GunnerLeo/Cryptid-Sledgfire-Pump-Action-Clip-Fed-Conversion/Cryptid Clips STL Files/Mega Clips/10 Shot Mega.stl

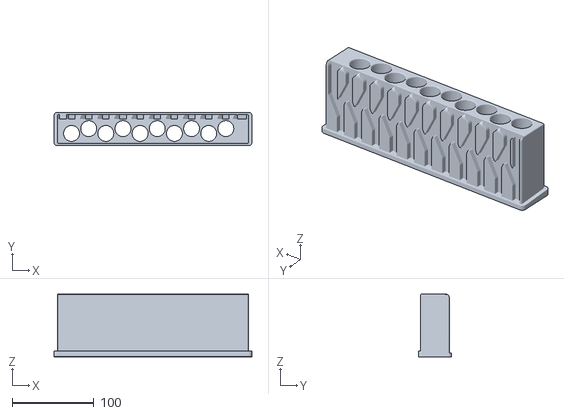
[picture p20: CAD file, 2022-12-31]
Cryptid Clips STL Files/Mega Clips/10 Shot Mega.stl
242.4 x 41.0 x 77.0
