GunnerLeo/Cryptid-Sledgfire-Pump-Action-Clip-Fed-Conversion/Cryptid Clips STL Files/Single Shot Clips/10 Shot Single.stl

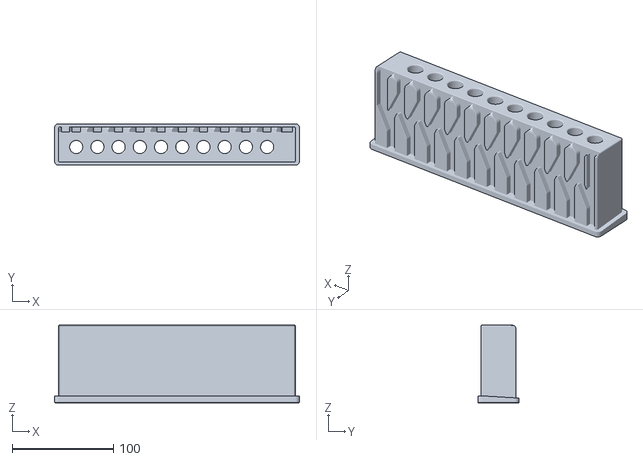
[picture p21: CAD file, 2022-12-31]
Cryptid Clips STL Files/Single Shot Clips/10 Shot Single.stl
242.4 x 41.0 x 77.0
