GunnerLeo/Cryptid-Sledgfire-Pump-Action-Clip-Fed-Conversion/Cryptid STL Files/Manacles.stl

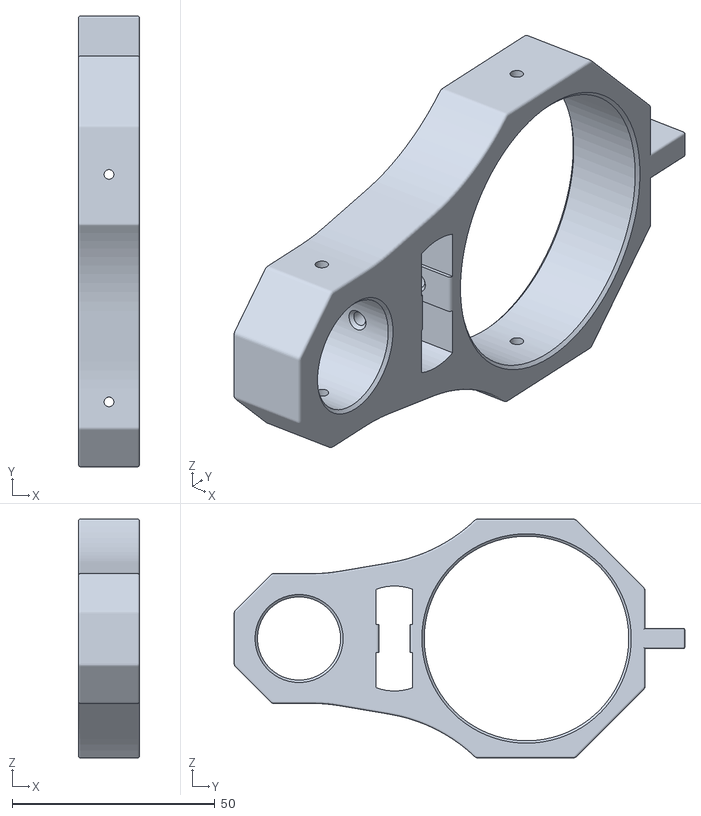
[picture p22: CAD file, 2022-12-30]
Cryptid STL Files/Manacles.stl
15.0 x 111.1 x 58.9
