GunnerLeo/Cryptid-Sledgfire-Pump-Action-Clip-Fed-Conversion/Cryptid STL Files/LongHinge1.stl

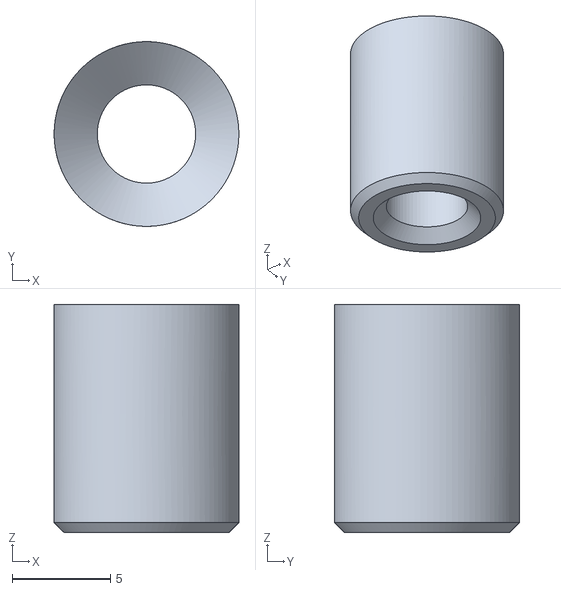
[picture p23: CAD file, 2022-12-30]
Cryptid STL Files/LongHinge1.stl
9.40 x 9.40 x 11.6
