GunnerLeo/Cryptid-Sledgfire-Pump-Action-Clip-Fed-Conversion/Cryptid STL Files/Latch Replacement.stl

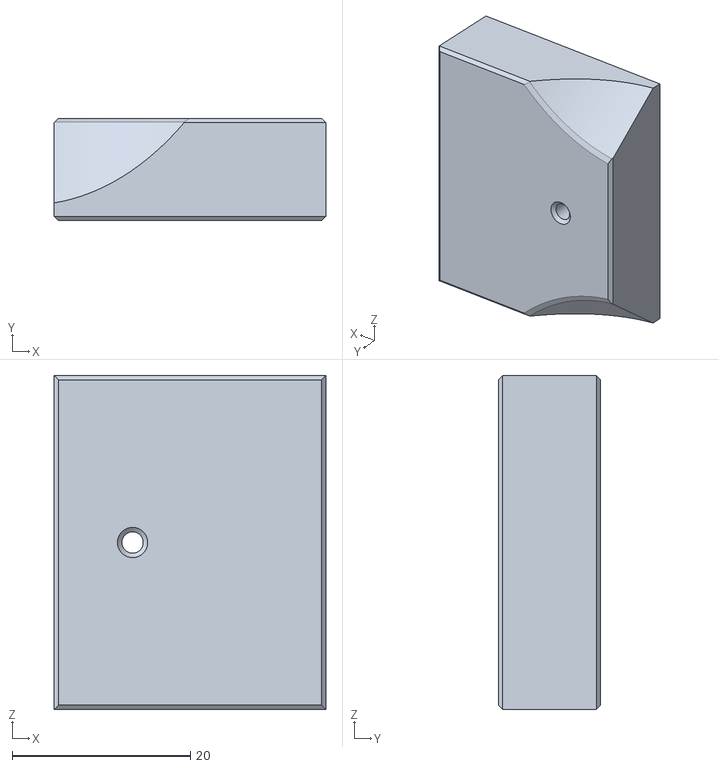
[picture p24: CAD file, 2022-12-30]
Cryptid STL Files/Latch Replacement.stl
30.5 x 11.5 x 37.5
