GunnerLeo/Cryptid-Sledgfire-Pump-Action-Clip-Fed-Conversion/Cryptid STL Files/ConnectorArm.stl

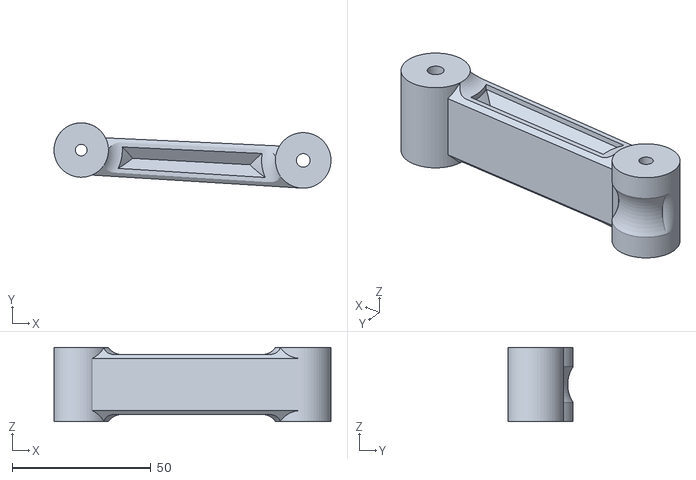
[picture p25: CAD file, 2022-12-30]
Cryptid STL Files/ConnectorArm.stl
99.7 x 23.5 x 26.7
