GunnerLeo/Cryptid-Sledgfire-Pump-Action-Clip-Fed-Conversion/Cryptid STL Files/WIshbone.stl

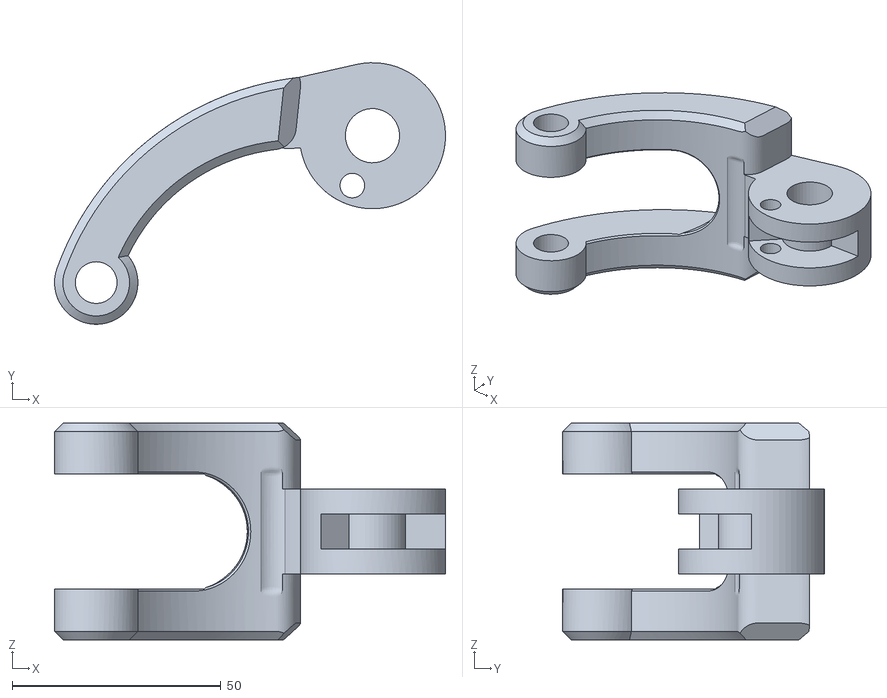
[picture p26: CAD file, 2022-12-30]
Cryptid STL Files/WIshbone.stl
93.7 x 62.7 x 51.9
