GunnerLeo/Cryptid-Sledgfire-Pump-Action-Clip-Fed-Conversion/Cryptid STL Files/Retainer Notch.stl

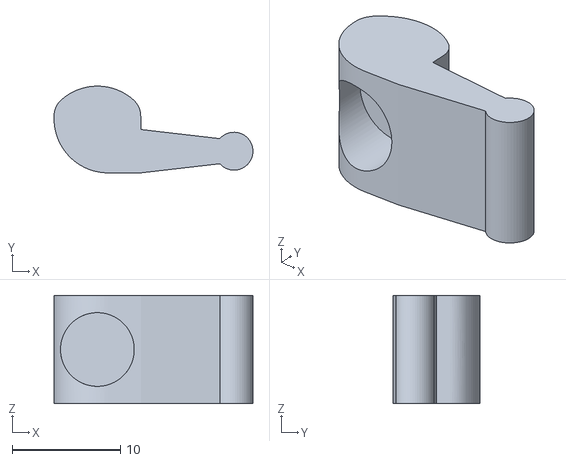
[picture p27: CAD file, 2022-12-30]
Cryptid STL Files/Retainer Notch.stl
18.4 x 8.00 x 10.0
