GunnerLeo/Cryptid-Sledgfire-Pump-Action-Clip-Fed-Conversion/Cryptid STL Files/Clipwell.stl

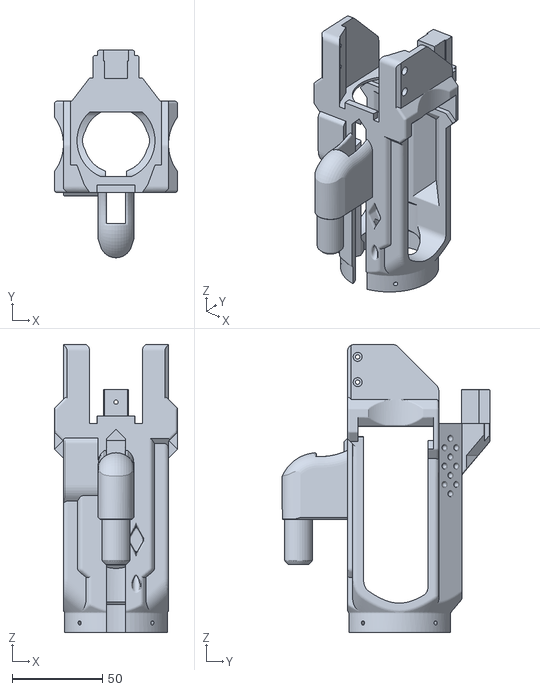
[picture p28: CAD file, 2022-12-30]
Cryptid STL Files/Clipwell.stl
68.2 x 114.9 x 159.4
