GunnerLeo/Cryptid-Sledgfire-Pump-Action-Clip-Fed-Conversion/Cryptid STL Files/ShortHinge1.stl

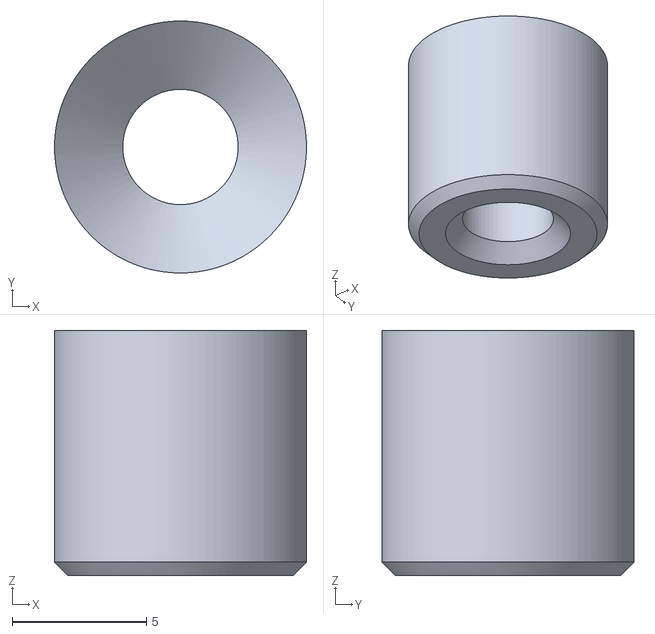
[picture p29: CAD file, 2022-12-30]
Cryptid STL Files/ShortHinge1.stl
9.40 x 9.40 x 9.15
