GunnerLeo/Cryptid-Sledgfire-Pump-Action-Clip-Fed-Conversion/Cryptid STL Files/Cam Arm.stl

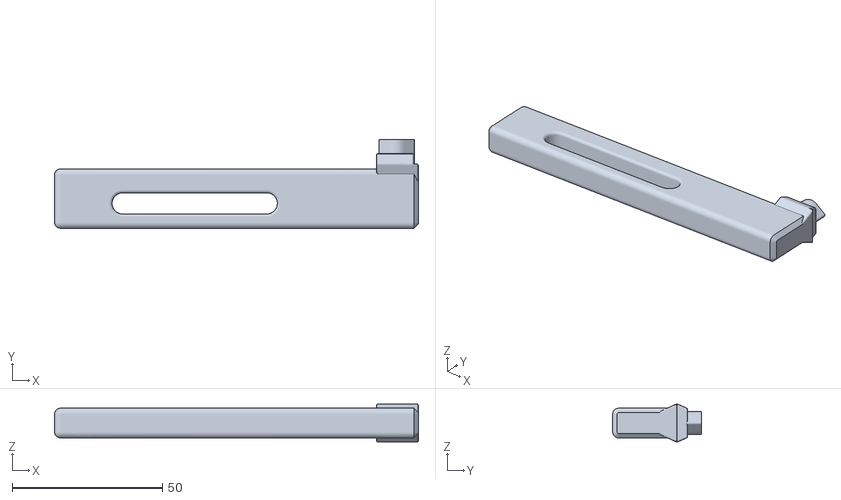
[picture p30: CAD file, 2022-12-30]
Cryptid STL Files/Cam Arm.stl
121.2 x 29.5 x 12.6
