GunnerLeo/Cryptid-Sledgfire-Pump-Action-Clip-Fed-Conversion/Cryptid STL Files/PumpBody.stl

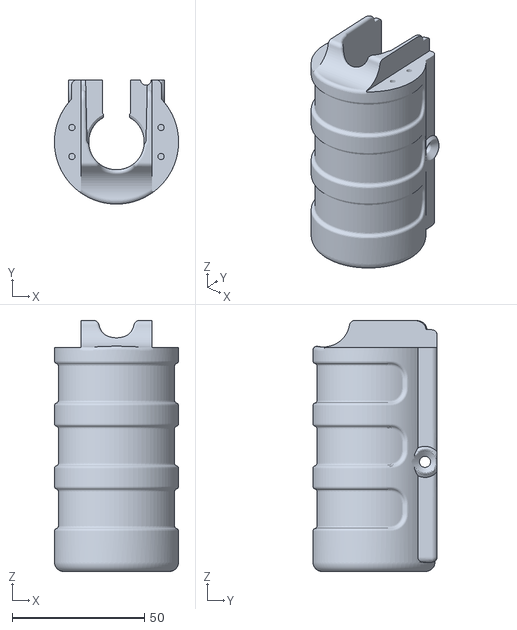
[picture p31: CAD file, 2022-12-30]
Cryptid STL Files/PumpBody.stl
47.0 x 47.0 x 95.0
