GunnerLeo/Cryptid-Sledgfire-Pump-Action-Clip-Fed-Conversion/Cryptid STL Files/Retainer Notch Clip.stl

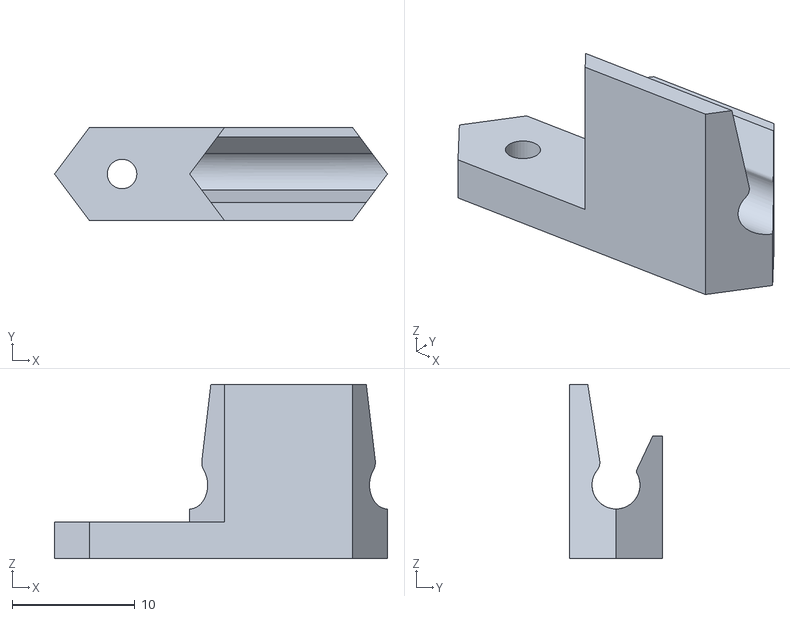
[picture p32: CAD file, 2022-12-30]
Cryptid STL Files/Retainer Notch Clip.stl
27.1 x 7.60 x 14.2
